sjgray/cbmSD/passthru/pass-c2e/Pics/2025-12-01-Render-top.jpg

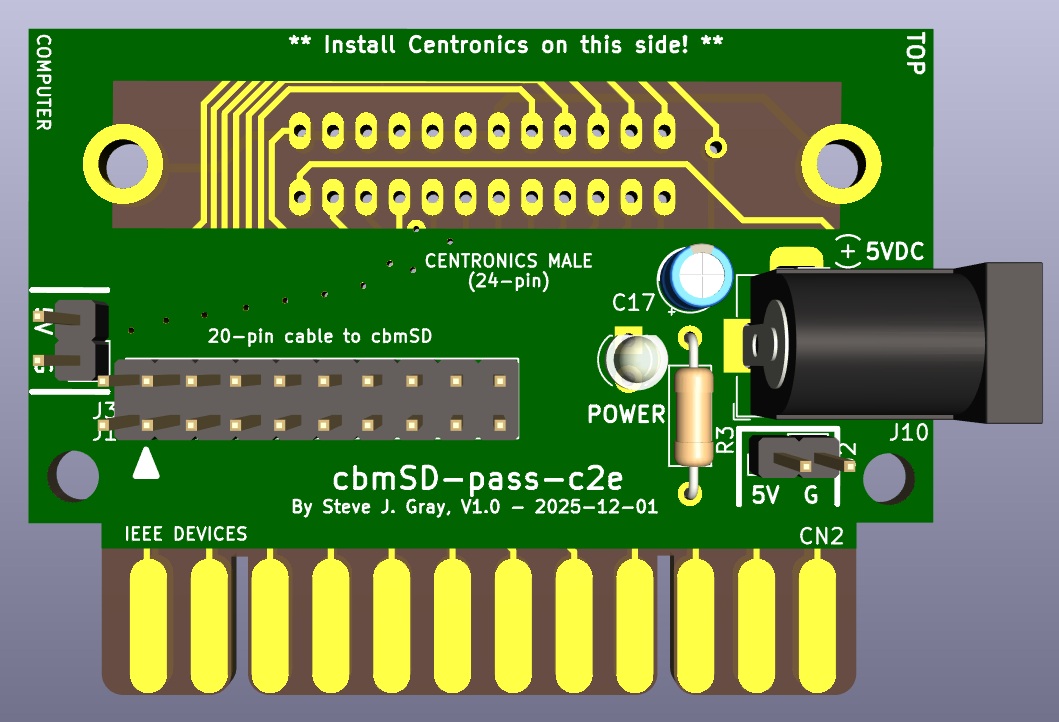
passthru/pass-c2e/Pics/2025-12-01-Render-top.jpg
