sjgray/cbmSD/passthru/pass-e2e/Pics/cbmSD-pass-render.jpg

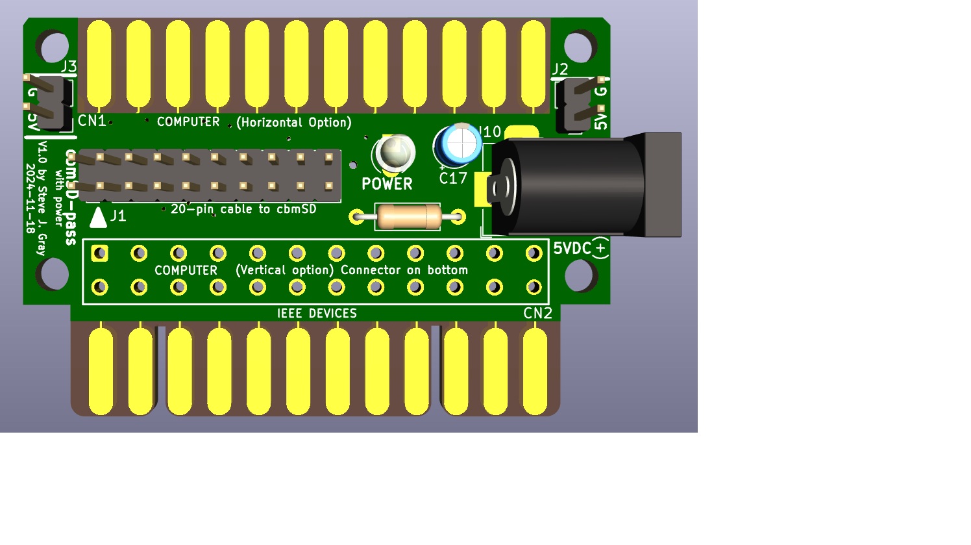
passthru/pass-e2e/Pics/cbmSD-pass-render.jpg
