sjgray/cbmSD/xd/v1/Pics/render.jpg

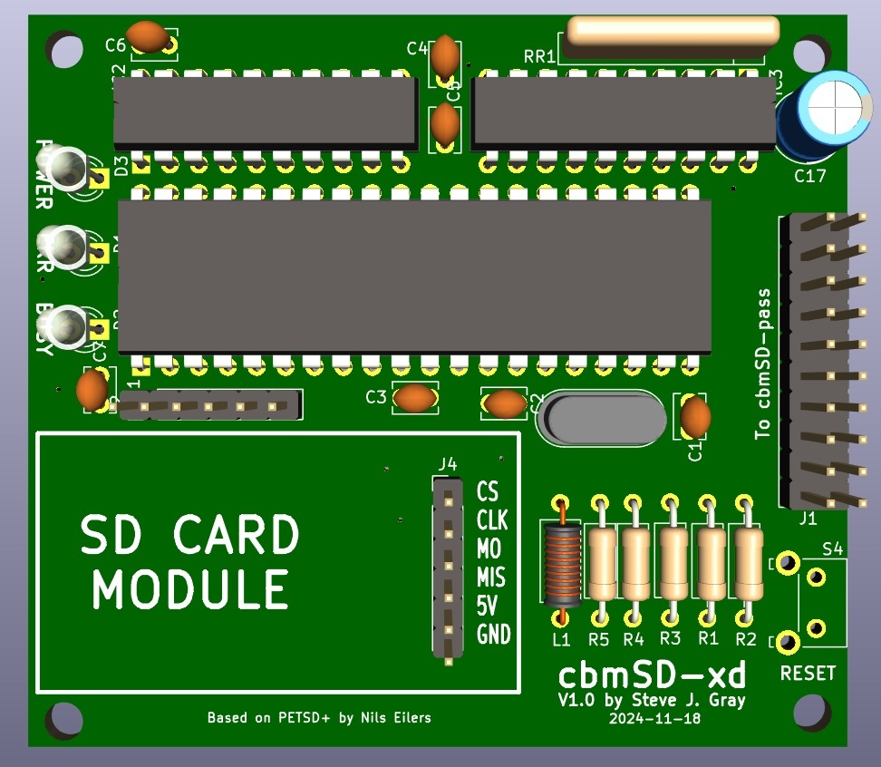
xd/v1/Pics/render.jpg
