sjgray/cbmSD/xd/v1/Pics/routing.jpg

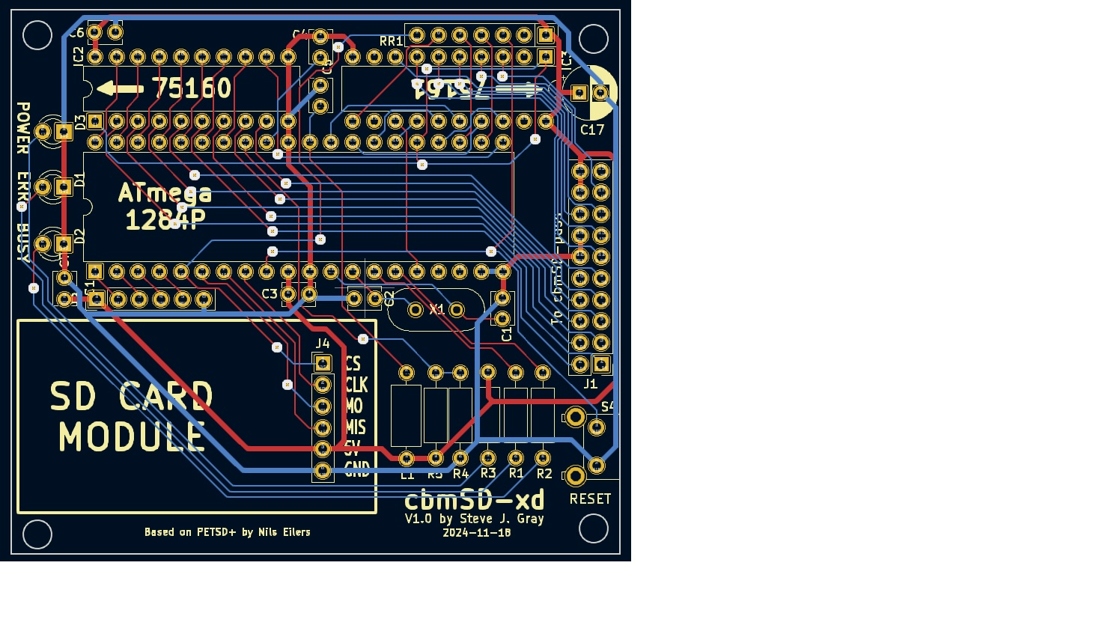
xd/v1/Pics/routing.jpg
